sparkfun/Teensy_3_1_XBee_Adapter/Documentation/Notated_board.png

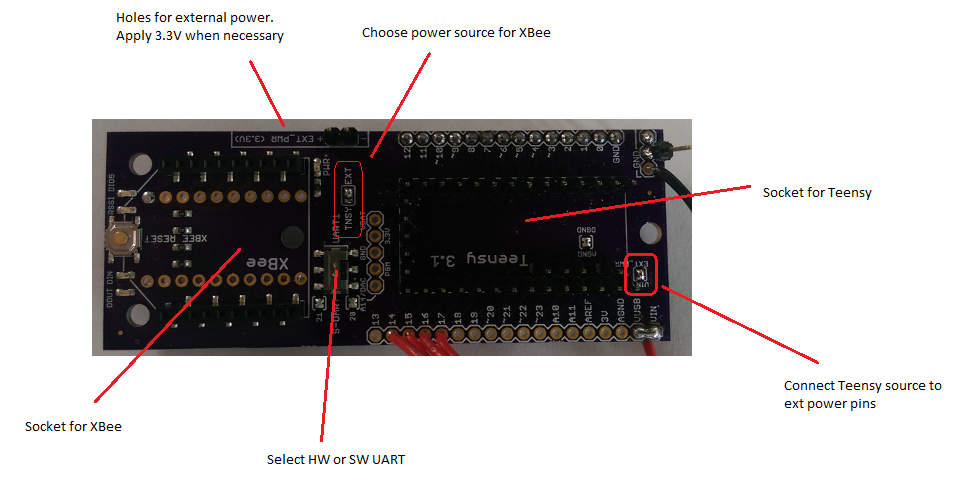
Documentation/Notated_board.png
