sparkfun/Teensy_3_1_XBee_Adapter/Documentation/PO2.png

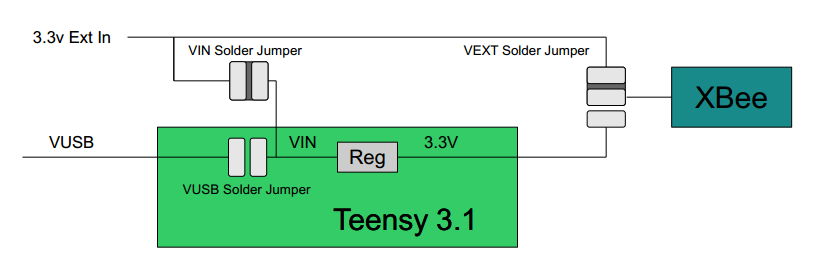
Documentation/PO2.png
